Hengy/Embedded-Controller-ESE2/Code/TIM16.h

#ifndef __TIM16_H
#define __TIM16_H

#include "stm32f30xe.h"
#include "utils.h"

// servo signal frequency
#define STEP_PWMFREQFAST			78		// ~1024Hz
#define STEP_PWMFREQMED				280		// ~128Hz
#define STEP_PWMFREQSLOW			1561	// ~64Hz

void TIM16_Init(uint16_t freq);
void TIM16_set(uint16_t freq);
void TIM16_enable(void);
void TIM16_disable(void);

#endif /* __TIM16_H */
